pete-restall/JunkBoxMsf/Firmware/JunkBoxMsf.h

#ifndef __JUNKBOXMSF_JUNKBOXMSF_H
#define	__JUNKBOXMSF_JUNKBOXMSF_H

#define DEBUG_RECEIVER_STUB_DATE_AND_TIME 0

#define NO_CALLBACK 0

typedef enum
{
	UpdateStatus_Idle,
	UpdateStatus_MoreWorkQueued
} UpdateStatus;

#endif
